Duke306/openace/doc/img/868mhz-antenna-openscad.png

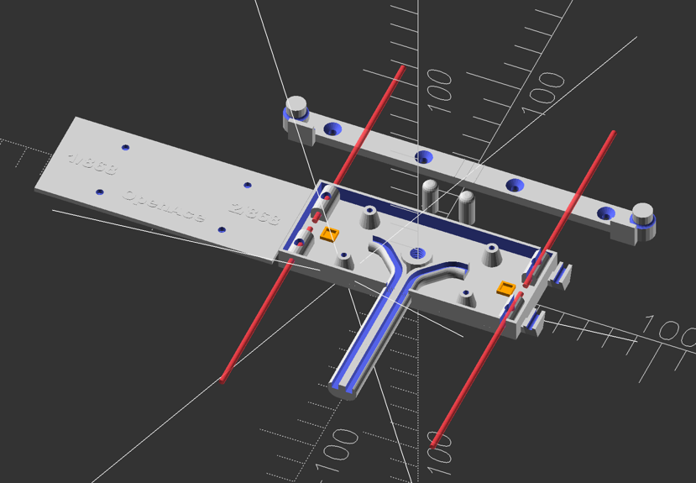
doc/img/868mhz-antenna-openscad.png
