Duke306/openace/doc/img/docker-add-resource.jpg

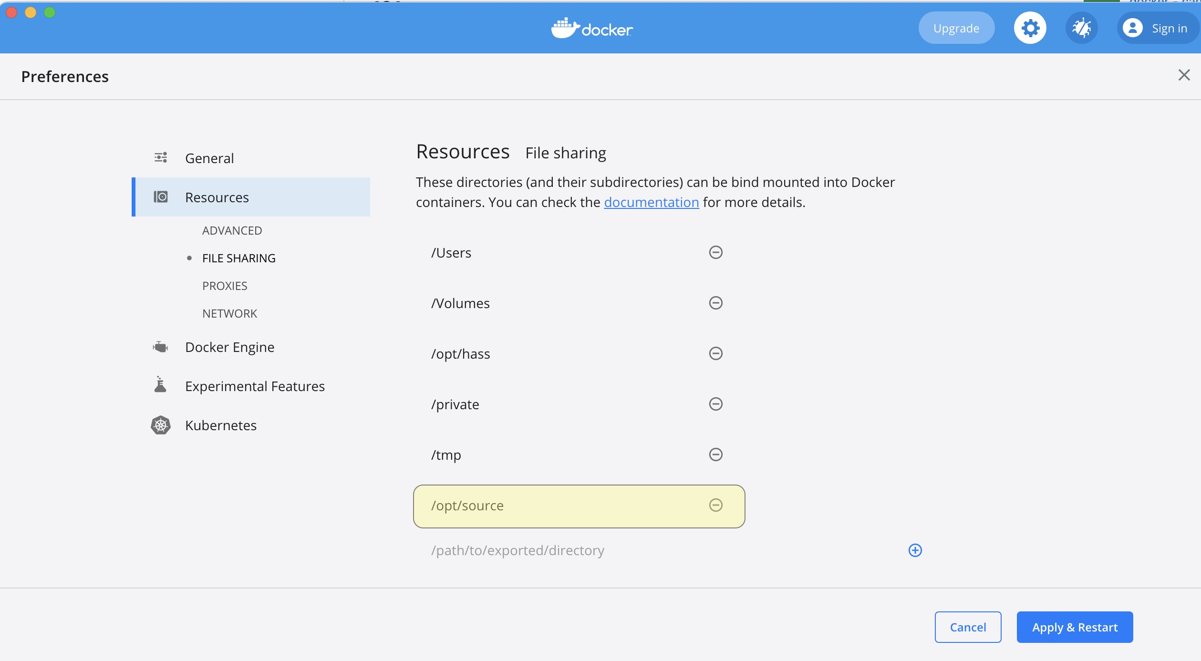
doc/img/docker-add-resource.jpg
