Duke306/openace/doc/img/gps-antenna-prusa.png

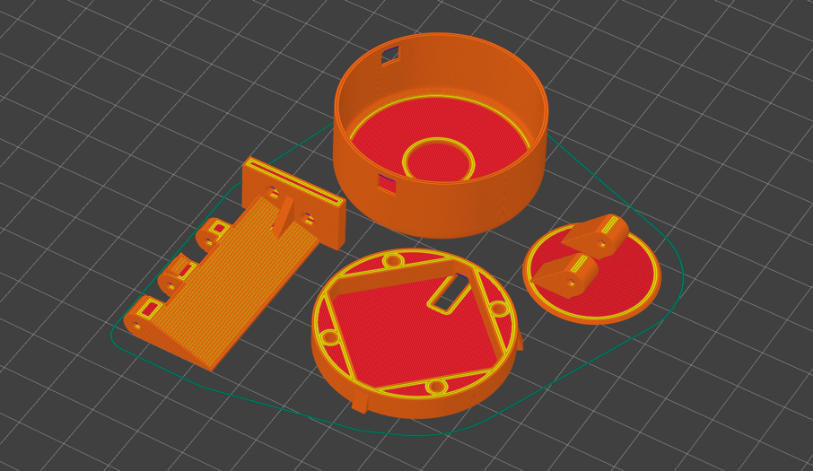
doc/img/gps-antenna-prusa.png
