Duke306/openace/doc/img/kicadpcb.jpg

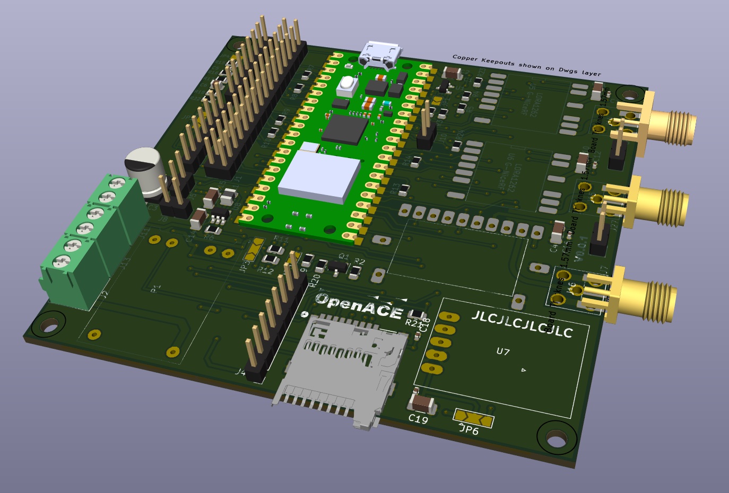
doc/img/kicadpcb.jpg
