Duke306/openace/doc/img/openscadopen.jpg

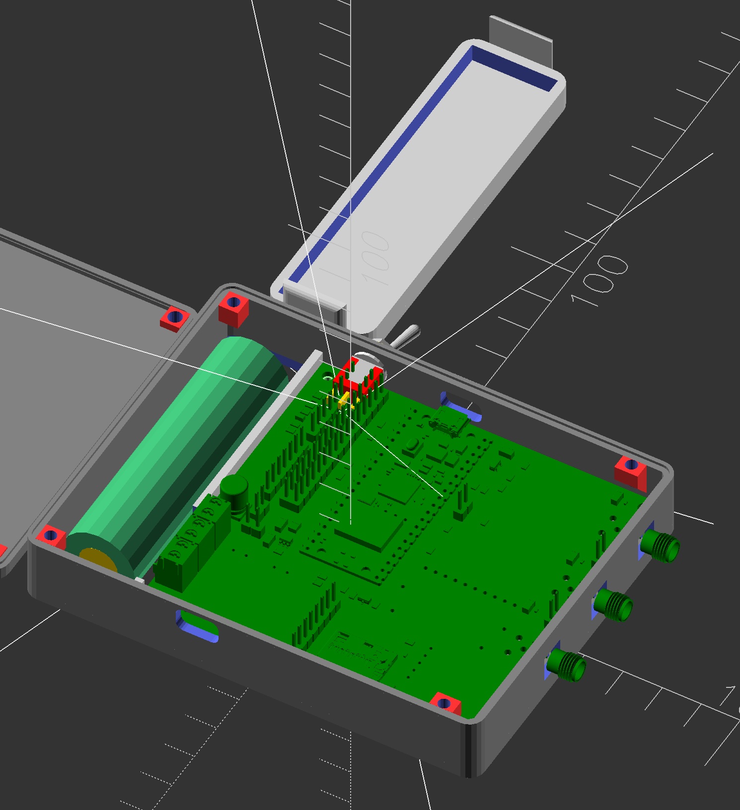
doc/img/openscadopen.jpg
