Duke306/openace/doc/img/Pico-bootsel.png

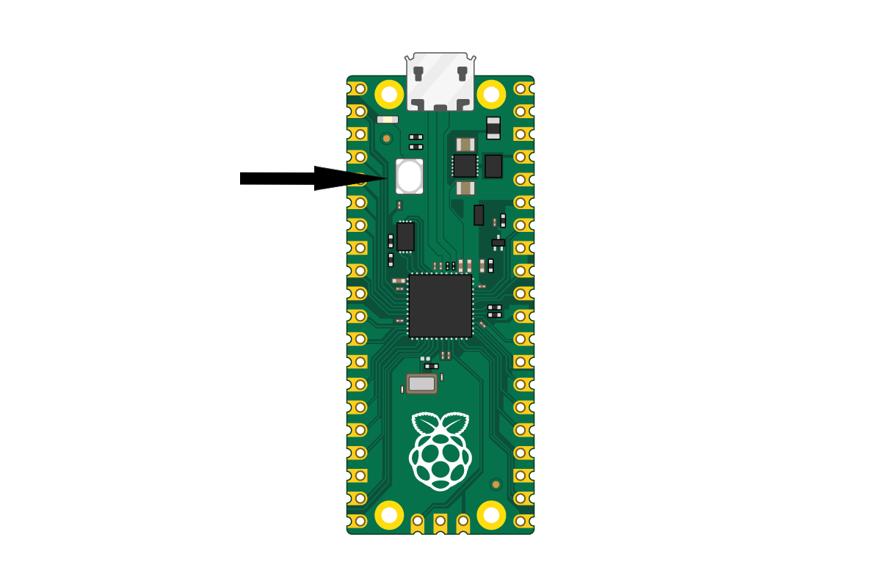
doc/img/Pico-bootsel.png
