Duke306/openace/doc/img/prusa-slicer.png

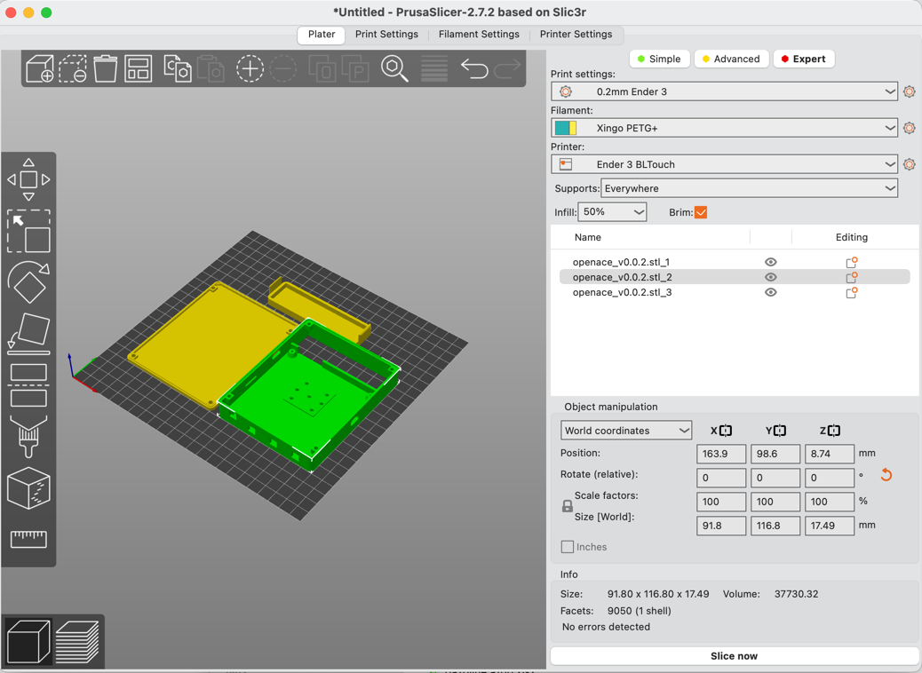
doc/img/prusa-slicer.png
