Duke306/openace/doc/media/gatas-dark.png

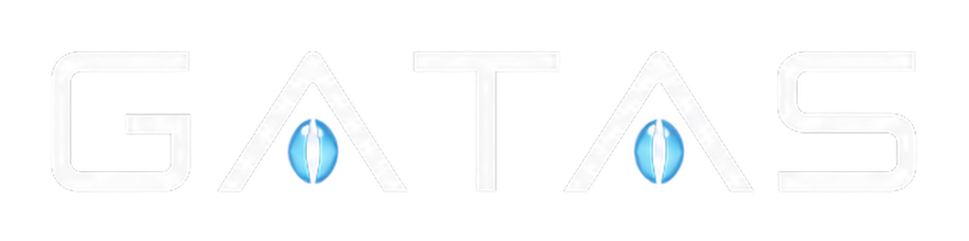
doc/media/gatas-dark.png
