Duke306/openace/doc/media/gatas-light.png

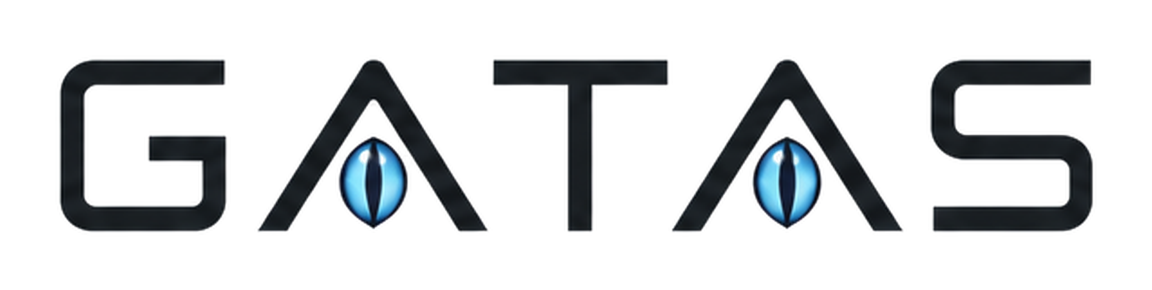
doc/media/gatas-light.png
