Duke306/openace/OpenACE V0.0.2/img.png

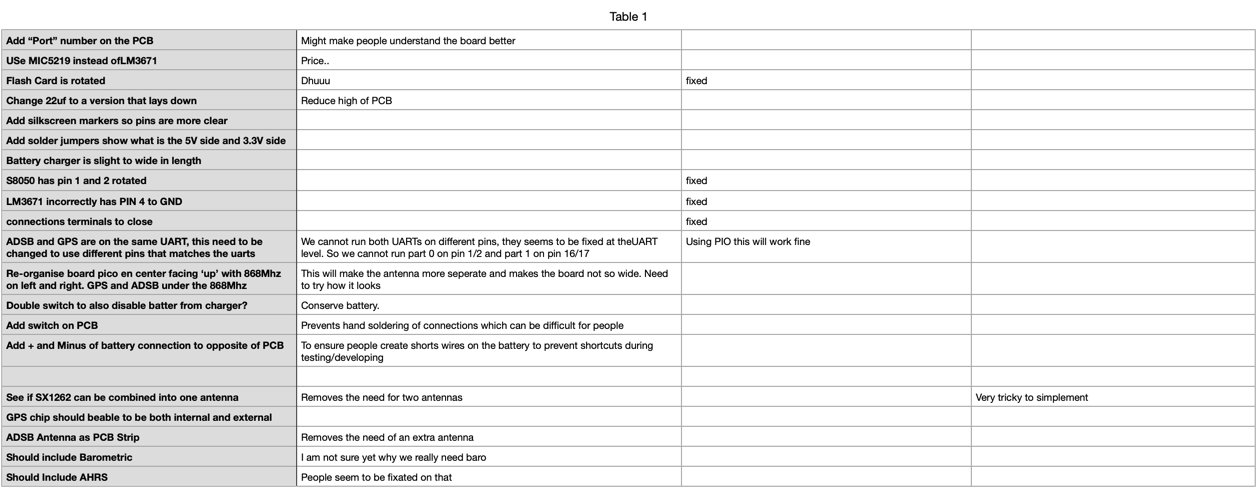
OpenACE V0.0.2/img.png
